crbyxwpzfl/fpaper/test/xpwallpaper.h

const unsigned char epd_bitmap_xpwallp [] PROGMEM = {
	0xb3, 0x36, 0xed, 0xbf, 0xff, 0xff, 0xef, 0xff, 0xff, 0xff, 0xff, 0x66, 0x6f, 0xb9, 0x24, 0x92, 
	0x49, 0x24, 0x92, 0x4d, 0xb7, 0x6d, 0xb6, 0xff, 0xff, 0xff, 0xff, 0xff, 0xfb, 0x6c, 0x9b, 0x64, 
	0x00, 0x00, 0x00, 0x7c, 0x00, 0x00, 0x4c, 0x9a, 0x6d, 0xe5, 0xff, 0xff, 0xff, 0xfe, 0xff, 0xff, 
	0xff, 0xff, 0x2c, 0xc9, 0xa9, 0x93, 0x77, 0xff, 0xe4, 0xce, 0x5f, 0xff, 0xad, 0x99, 0x99, 0xcd, 
	0x9a, 0xcd, 0xad, 0x33, 0x6d, 0xb2, 0x65, 0xb5, 0x9b, 0x29, 0xb7, 0xff, 0xff, 0xfd, 0xb6, 0xb3, 
	0x62, 0x59, 0xb6, 0x66, 0x4c, 0x86, 0xc9, 0x4d, 0x13, 0x26, 0xb7, 0x37, 0x7f, 0xff, 0xff, 0xf3, 
	0xb7, 0xff, 0xff, 0xff, 0xc9, 0x29, 0x36, 0x6c, 0xdf, 0xa6, 0x76, 0xf3, 0x9f, 0xfb, 0xb6, 0xd3, 
	0x67, 0x72, 0x4a, 0x64, 0xa4, 0xc9, 0x24, 0x93, 0x59, 0x96, 0x69, 0xee, 0xec, 0xfe, 0xdb, 0x6f, 
	0xb6, 0x99, 0x2c, 0xda, 0x01, 0x11, 0x22, 0x10, 0x24, 0x41, 0x23, 0x24, 0xb6, 0xdb, 0xdf, 0xff, 
	0xff, 0xf6, 0x6f, 0x7f, 0xff, 0xff, 0x53, 0x66, 0xd2, 0x6d, 0xbb, 0xf1, 0x9b, 0x3f, 0xb6, 0x6e, 
	0xdb, 0x66, 0x6d, 0x6c, 0xc9, 0x32, 0x52, 0x4c, 0xb6, 0x4c, 0xda, 0x73, 0xee, 0x5b, 0x6f, 0x6f, 
	0xff, 0xfb, 0xfb, 0xcc, 0x93, 0x26, 0xc9, 0x11, 0x22, 0x49, 0x24, 0x92, 0x48, 0xd9, 0x6d, 0xde, 
	0xf7, 0xff, 0xff, 0xf9, 0x6b, 0xff, 0xff, 0xff, 0x5c, 0x9a, 0x4d, 0x93, 0x2e, 0xdd, 0xfb, 0xdd, 
	0xad, 0xbf, 0xd9, 0x99, 0x99, 0x99, 0x35, 0x8b, 0x5b, 0x33, 0x93, 0x69, 0x26, 0xcc, 0x9b, 0xd9, 
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
};

// Array of all bitmaps for convenience. (Total bytes used to store images in PROGMEM = 15024)
const int epd_bitmap_allArray_LEN = 1;
const unsigned char* epd_bitmap_allArray[1] = {
	epd_bitmap_xpwallp
};
